secretheadquarters/pager/docs/interface-module-pcb-buttons.png

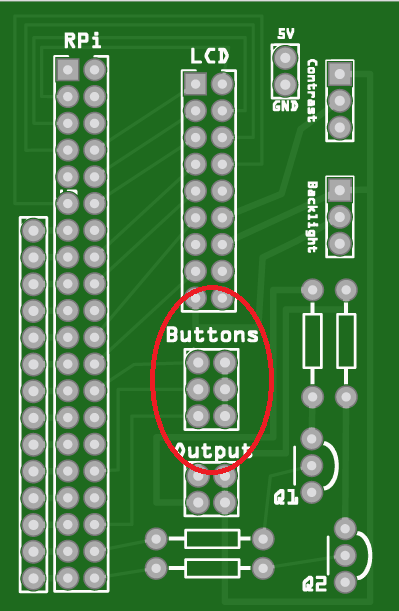
docs/interface-module-pcb-buttons.png
