secretheadquarters/pager/software/log.py

import logging
import logging.handlers

name = 'pager'
logger = logging.getLogger(name)
logger.setLevel(logging.DEBUG)

formatter = logging.Formatter('%(asctime)s - %(message)s')

log_filename = f"{name}.log"
fileHandler = logging.handlers.RotatingFileHandler(log_filename, maxBytes=1048576, backupCount=5)
fileHandler.setLevel(logging.DEBUG)
fileHandler.setFormatter(formatter)

# StreamHandler defaults to stderr
consoleHandler = logging.StreamHandler()
consoleHandler.setFormatter(formatter)

logger.addHandler(fileHandler)
logger.addHandler(consoleHandler)
